Moussycat/Projet_Neptune_Sense/Code/main_station_base/bitmaps.h

// 'wi-celsius', 22x20px
const unsigned char epd_bitmap_wi_celsius [] PROGMEM = {
	0x18, 0x03, 0xe0, 0x7e, 0x0f, 0xf0, 0xe6, 0x1f, 0x78, 0xc3, 0x18, 0x1c, 0xc3, 0x38, 0x0c, 0xe6, 
	0x30, 0x00, 0x7e, 0x30, 0x00, 0x18, 0x30, 0x00, 0x00, 0x30, 0x00, 0x00, 0x30, 0x00, 0x00, 0x30, 
	0x00, 0x00, 0x30, 0x00, 0x00, 0x30, 0x00, 0x00, 0x30, 0x00, 0x00, 0x38, 0x08, 0x00, 0x38, 0x1c, 
	0x00, 0x1c, 0x3c, 0x00, 0x0f, 0xf8, 0x00, 0x07, 0xf0, 0x00, 0x01, 0x80
};

// 'wi-day-cloudy', 80x80px
const unsigned char epd_bitmap_wi_day_cloudy [] PROGMEM = {
	0x00, 0x00, 0x00, 0x00, 0x00, 0x00, 0x00, 0x00, 0x00, 0x00, 0x00, 0x00, 0x00, 0x00, 0x00, 0x00, 
	0x00, 0x00, 0x00, 0x00, 0x00, 0x00, 0x00, 0x00, 0x00, 0x01, 0x00, 0x00, 0x00, 0x00, 0x00, 0x00, 
	0x00, 0x00, 0x00, 0x07, 0x80, 0x00, 0x00, 0x00, 0x00, 0x00, 0x00, 0x00, 0x00, 0x07, 0xc0, 0x00, 
	0x00, 0x00, 0x00, 0x00, 0x00, 0x00, 0x00, 0x07, 0xc0, 0x00, 0x00, 0x00, 0x00, 0x00, 0x00, 0x00, 
	0x00, 0x07, 0xc0, 0x00, 0x00, 0x00, 0x00, 0x00, 0x00, 0x00, 0x00, 0x07, 0xc0, 0x00, 0x00, 0x00, 
	0x00, 0x00, 0x00, 0x00, 0x00, 0x07, 0xc0, 0x00, 0x00, 0x00, 0x00, 0x00, 0x00, 0x00, 0x00, 0x07, 
	0xc0, 0x00, 0x00, 0x00, 0x00, 0x00, 0x00, 0x0c, 0x00, 0x07, 0xc0, 0x00, 0x60, 0x00, 0x00, 0x00, 
	0x00, 0x1e, 0x00, 0x03, 0x80, 0x00, 0xf0, 0x00, 0x00, 0x00, 0x00, 0x1f, 0x00, 0x00, 0x00, 0x01, 
	0xf0, 0x00, 0x00, 0x00, 0x00, 0x1f, 0x80, 0x00, 0x00, 0x03, 0xf0, 0x00, 0x00, 0x00, 0x00, 0x0f, 
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
	epd_bitmap_wi_day_lightning,  //Ligthning out of a cloud -> Thunderstorm
  epd_bitmap_wi_day_showers,  //Cloud with litle rain -> showers 
	epd_bitmap_wi_day_rain, //Cloud with rain -> Heavy rain
	epd_bitmap_wi_day_snow_wind,  //Cloud with snow flake -> Snow
};
