Moussycat/Projet_Neptune_Sense/Code/main_station_base/credential.h

#ifndef __CREDENTIAL_H__
#define __CREDENTIAL_H__
typedef struct {
    char* ssid;
    char* password;
}Credential;

const Credential credentials[6] = {
    {"SSID_1","PASSWORD_1"},
    {"SSID_2","PASSWORD_2"},
    {"SSID_3","PASSWORD_3"},
    {"SSID_4","PASSWORD_4"}
};
#define SERVER_MQTT "XXXXXXXXXXXXXXXX"
#define USER_MQTT "XXXXXXXXXXXXXXXX"
#define PASS_MQTT "XXXXXXXXXXXXXXXX"
#define WEATHER_TOKEN "XXXXXXXX"

#endif
