Moussycat/Projet_Neptune_Sense/Code/main_station_base/master_time.h

#include "Arduino.h"
#include "time.h"
#include "sntp.h"
#include "config.h"

#ifndef TIMEMASTER_H
#define TIMEMASTER_H

class TimeM {
    public:
        int year;
        int month;
        int day;
        int min;
        int hour;
        int second;
        int daylight_saving;

        TimeM(void);
        void init(void);

        bool update_time(void);

    private:
        #if DEV
        static void timeavailable(struct timeval *t);
        #endif
};
#endif
