Moussycat/Projet_Neptune_Sense/Code/main_station_base/weather.h

#include "Arduino.h"
//config
#include "config.h"

//libraries
#include <HTTPClient.h>
#include <WiFiClient.h>
#include <Arduino_JSON.h>

#ifndef WEATHER_H
#define WEATHER_H

typedef enum{
  sunny = 0,
  cloudy,
  thunder,
  showers,
  rain,
  snow,
}WeatherIcon;

class Weather{
    public:
      String city;
      int sky;
      int temp;

      Weather(void);
      void init(void);
      void get_info(void);

    private:

      void update_info(void);
      String httpGETRequest(const char*);
      JSONVar formatAPI(void);


};
#endif
